Cuttlerat/zmk-config-lynxware-cat/img/IMG_1715.JPG

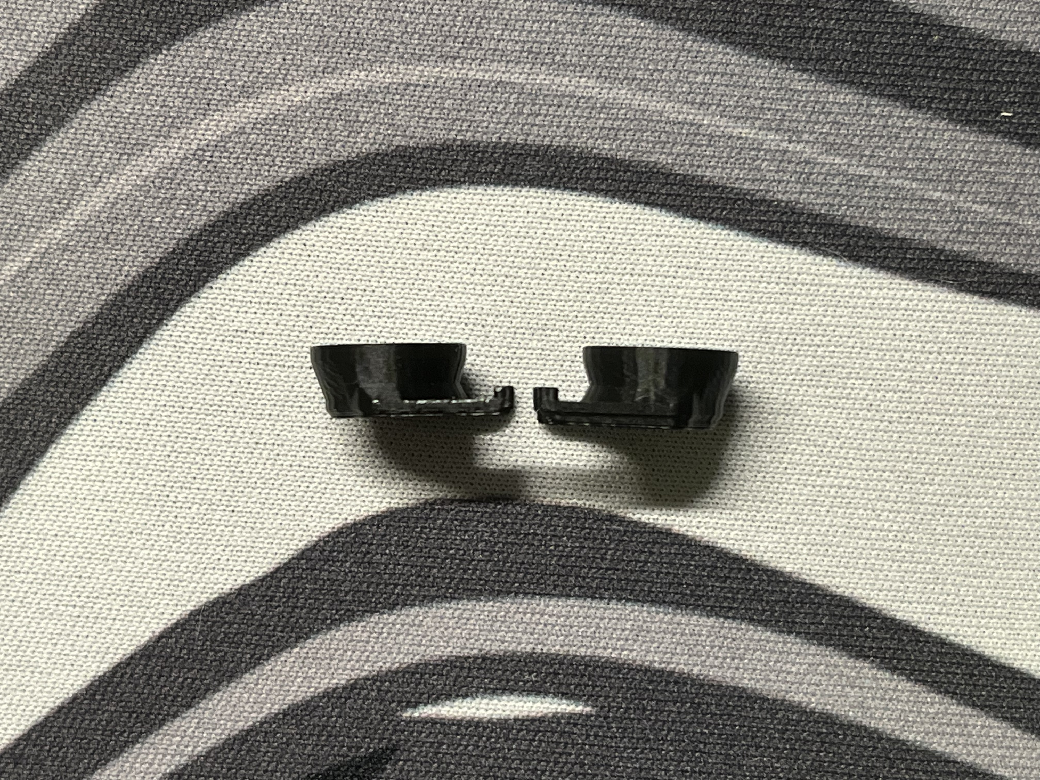
img/IMG_1715.JPG
