Cuttlerat/zmk-config-lynxware-cat/img/IMG_1717.JPG

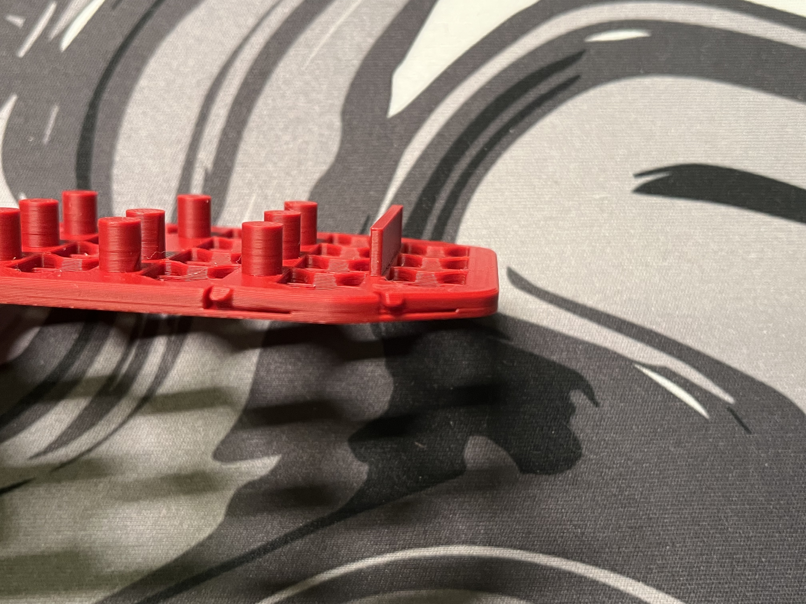
img/IMG_1717.JPG
