Cuttlerat/zmk-config-lynxware-cat/img/IMG_1721.JPG

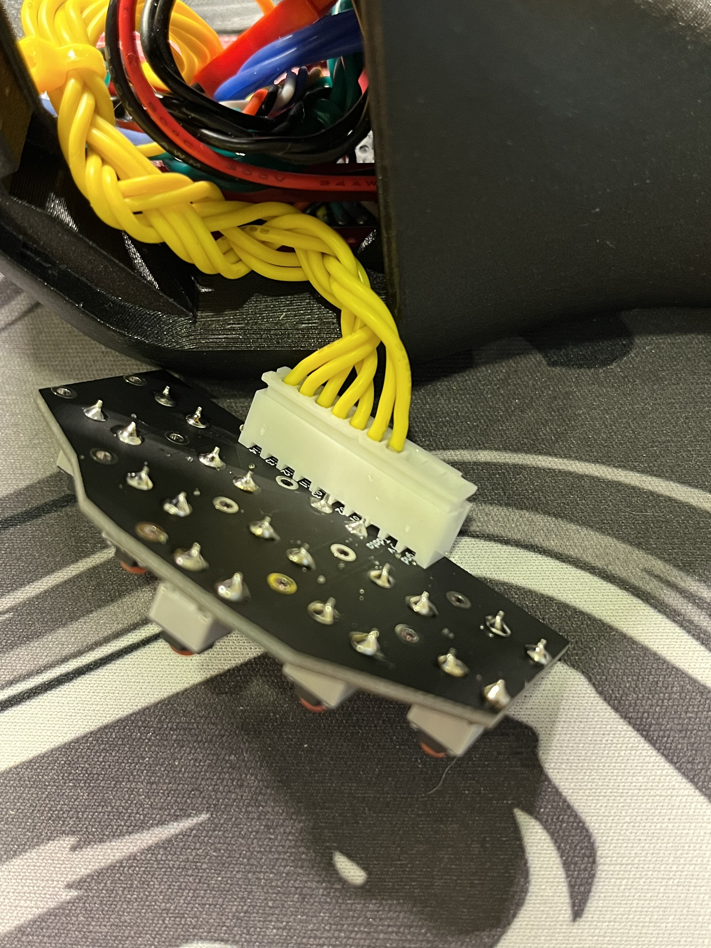
img/IMG_1721.JPG
