Cuttlerat/zmk-config-lynxware-cat/img/IMG_1724.JPG

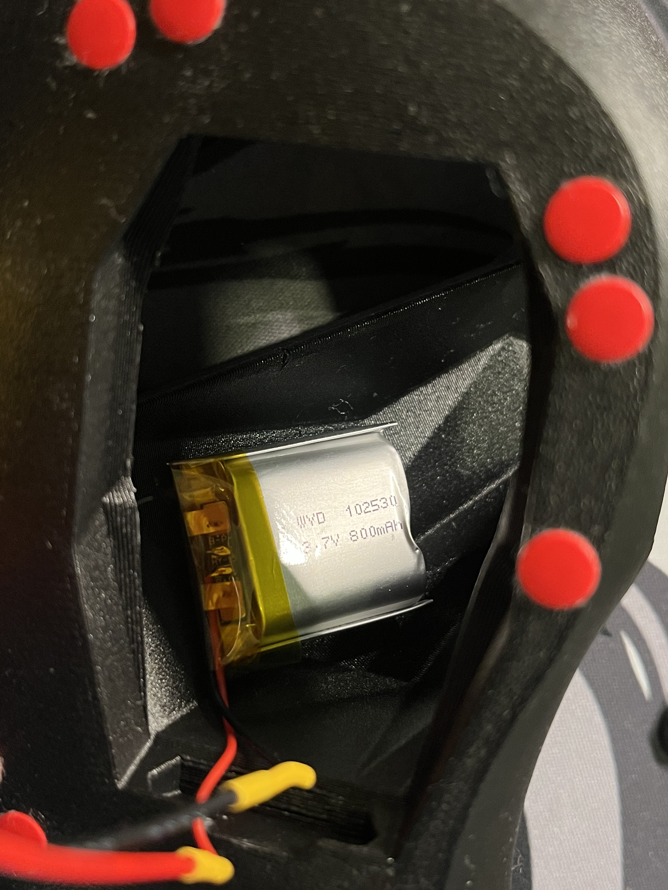
img/IMG_1724.JPG
