Cuttlerat/zmk-config-lynxware-cat/img/IMG_1726.JPG

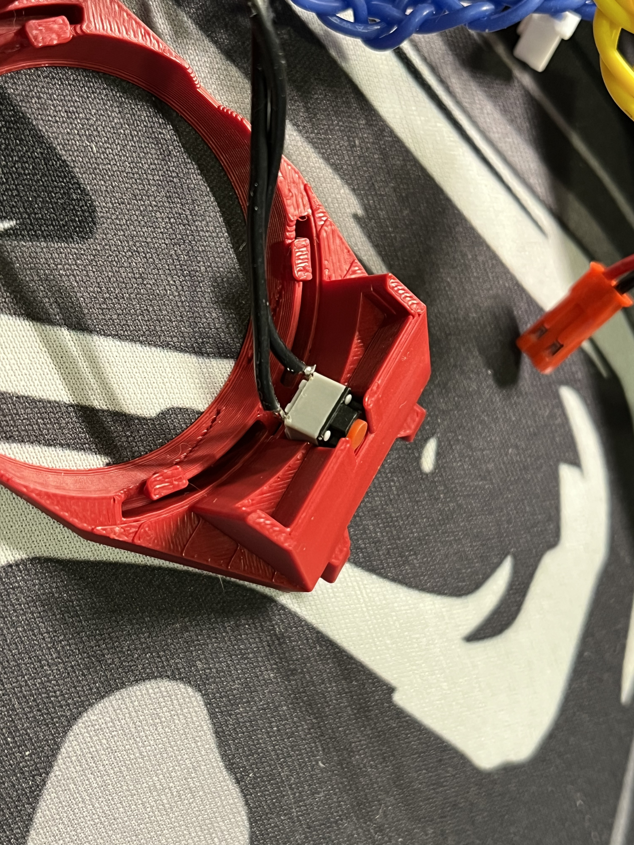
img/IMG_1726.JPG
