Cuttlerat/zmk-config-lynxware-cat/img/IMG_1730.JPG

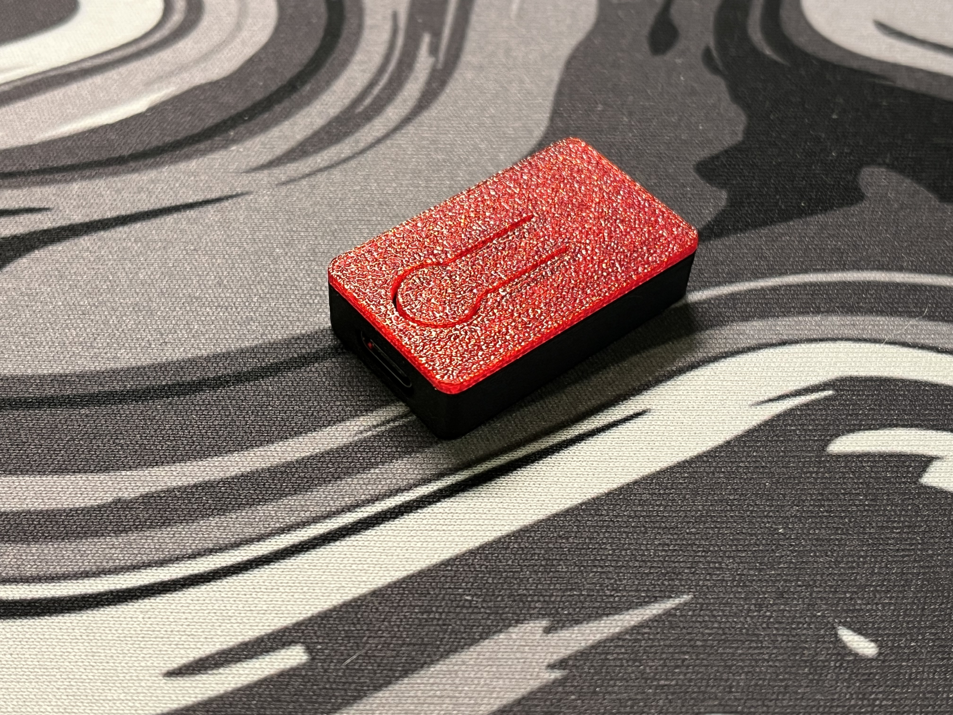
img/IMG_1730.JPG
