Cuttlerat/zmk-config-lynxware-cat/img/IMG_1732.JPG

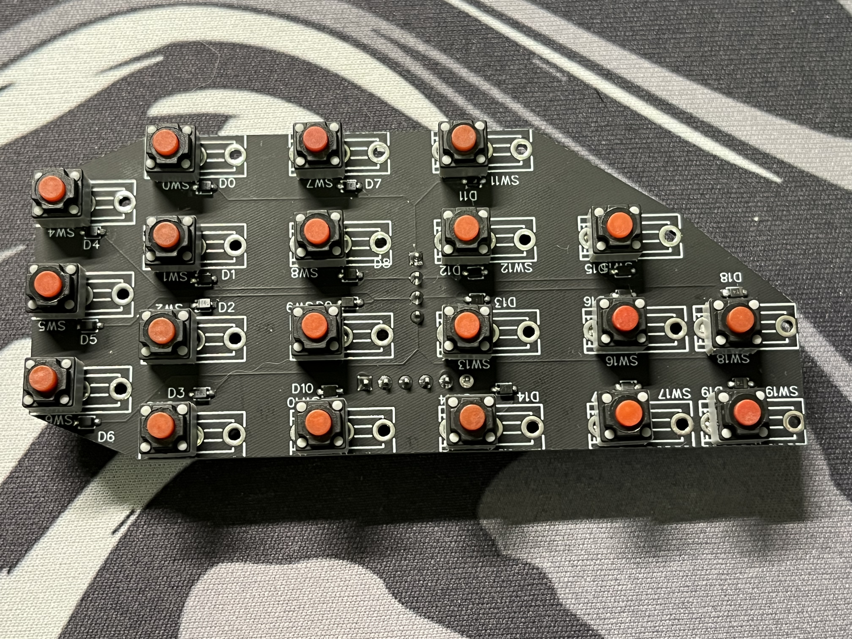
img/IMG_1732.JPG
