Cuttlerat/zmk-config-lynxware-cat/img/IMG_1733.JPG

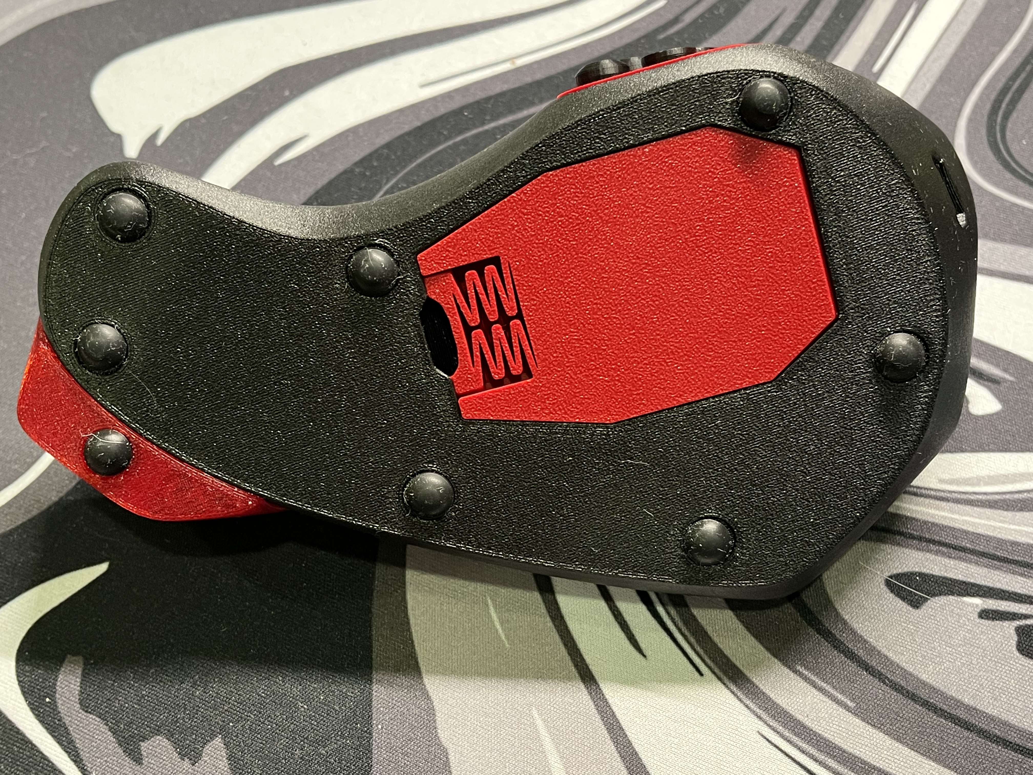
img/IMG_1733.JPG
