Cuttlerat/zmk-config-lynxware-cat/img/IMG_1734.JPG

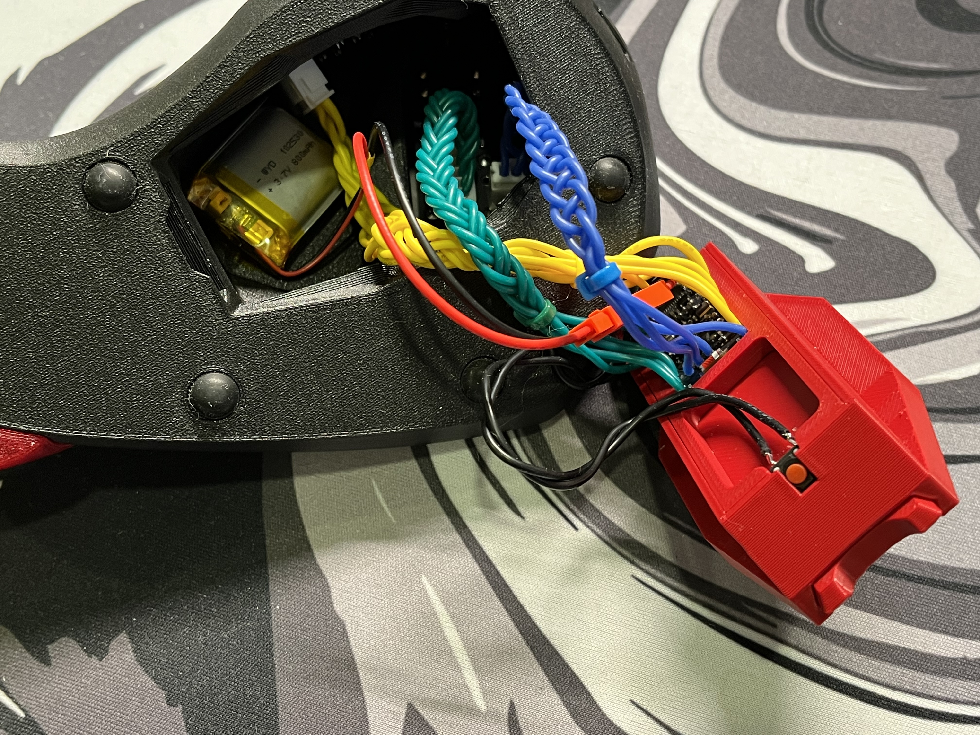
img/IMG_1734.JPG
