Cuttlerat/zmk-config-lynxware-cat/img/IMG_1735.JPG

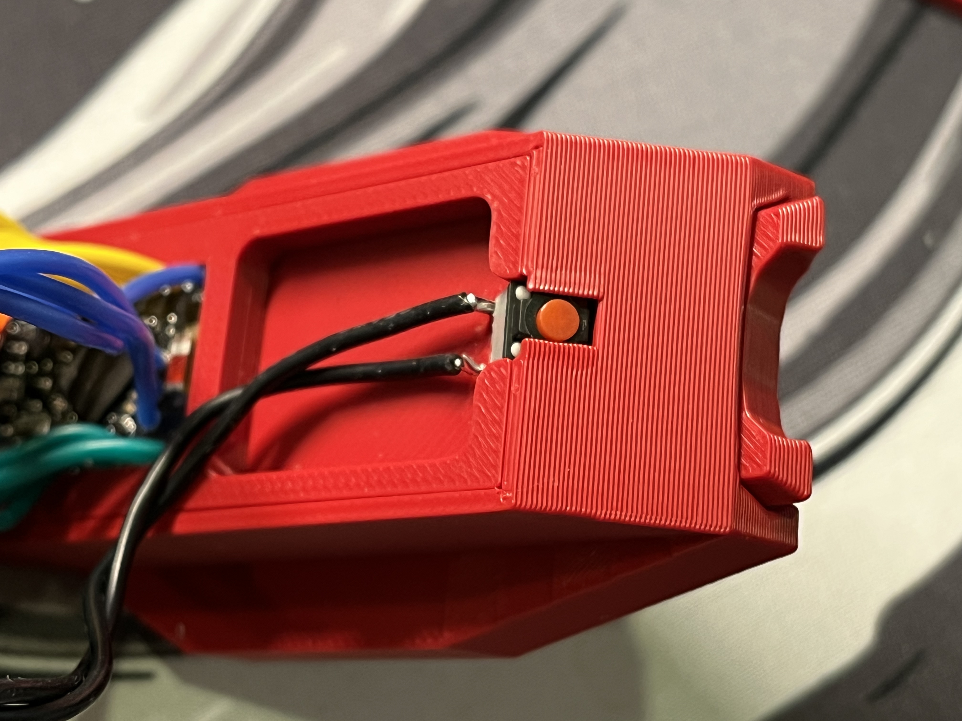
img/IMG_1735.JPG
