Cuttlerat/zmk-config-lynxware-cat/img/IMG_1719.JPG

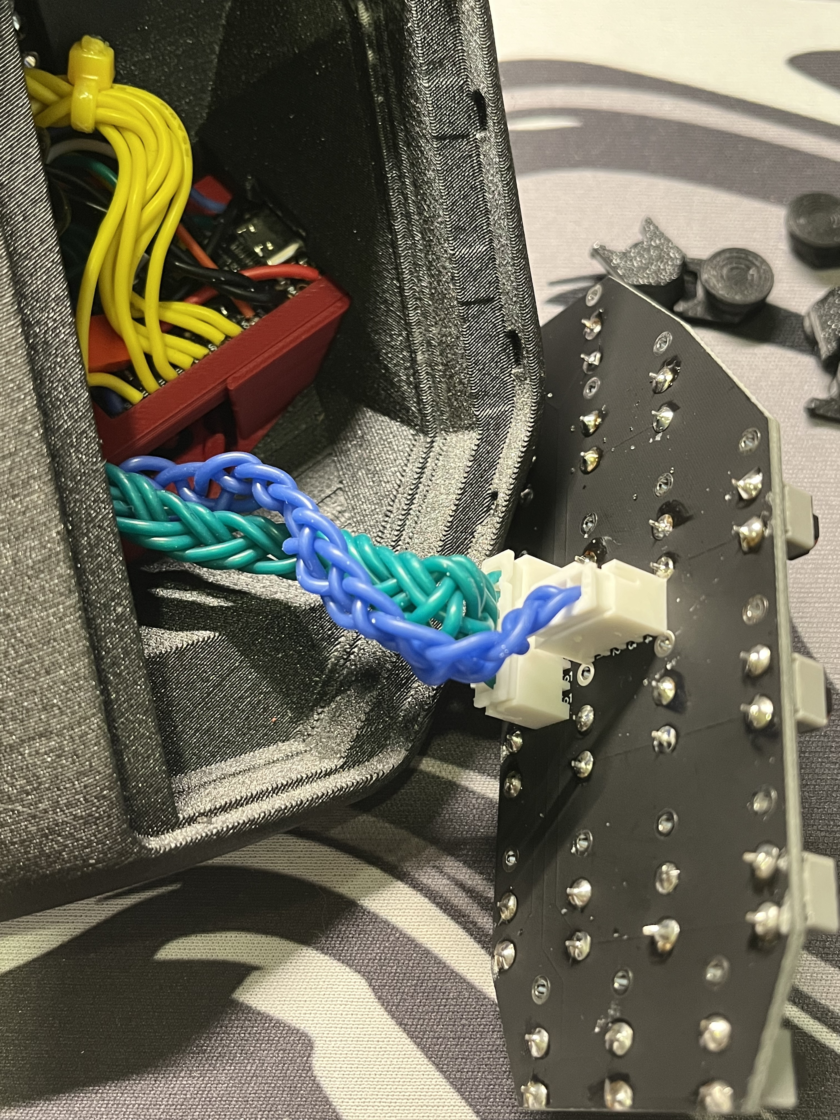
img/IMG_1719.JPG
