Cuttlerat/zmk-config-lynxware-cat/img/IMG_1722.JPG

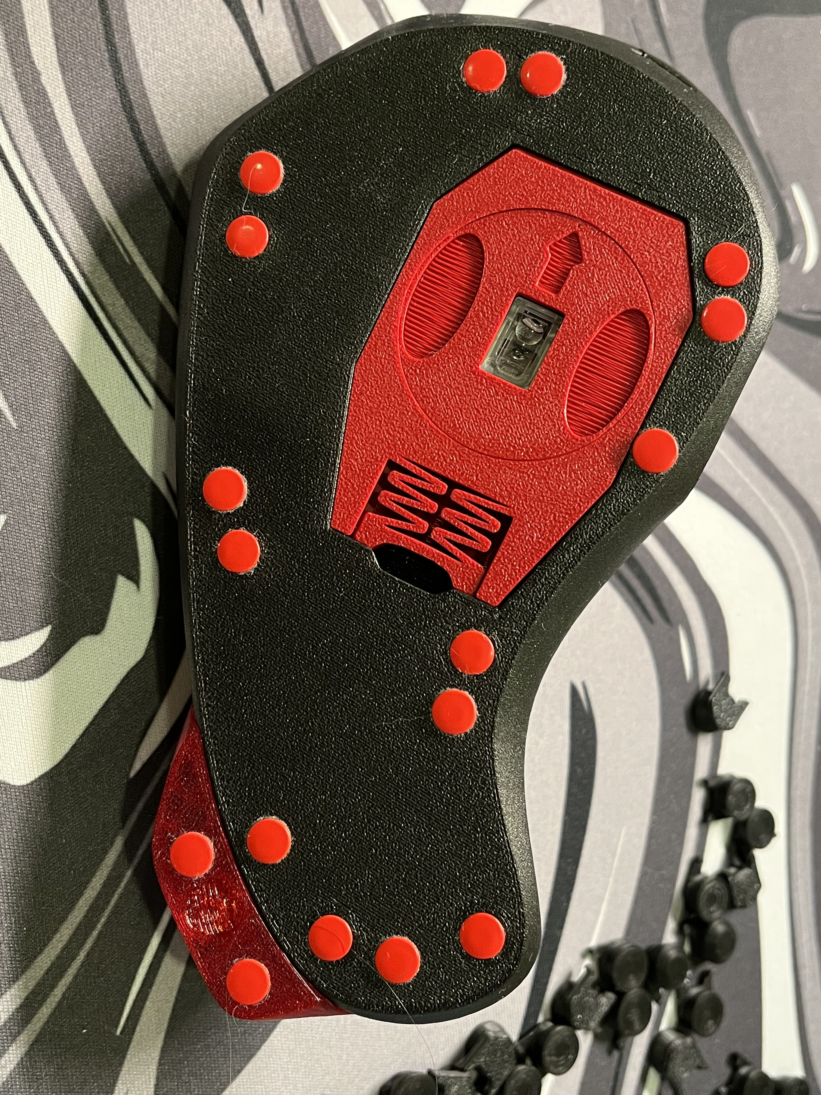
img/IMG_1722.JPG
