Cuttlerat/zmk-config-lynxware-cat/img/IMG_1723.JPG

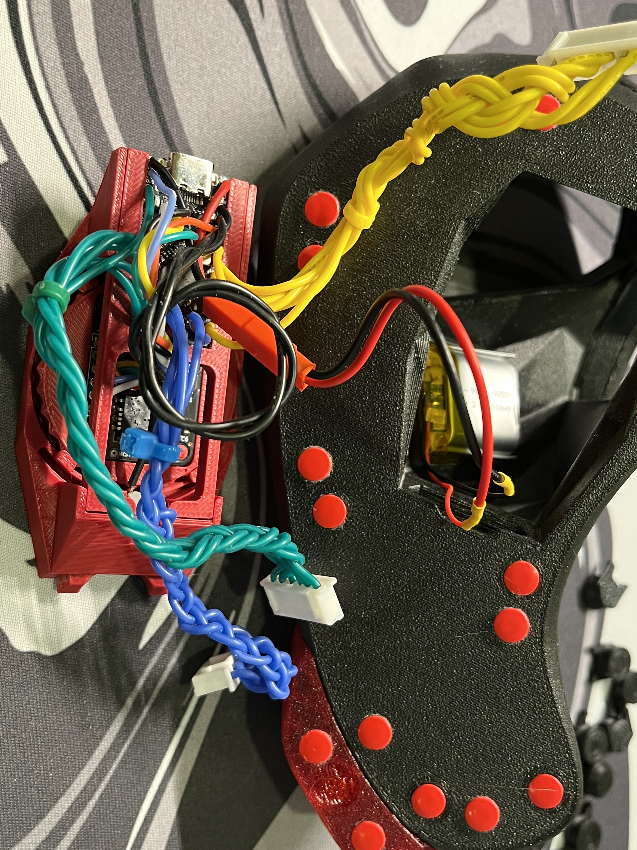
img/IMG_1723.JPG
