Cuttlerat/zmk-config-lynxware-cat/img/IMG_1725.JPG

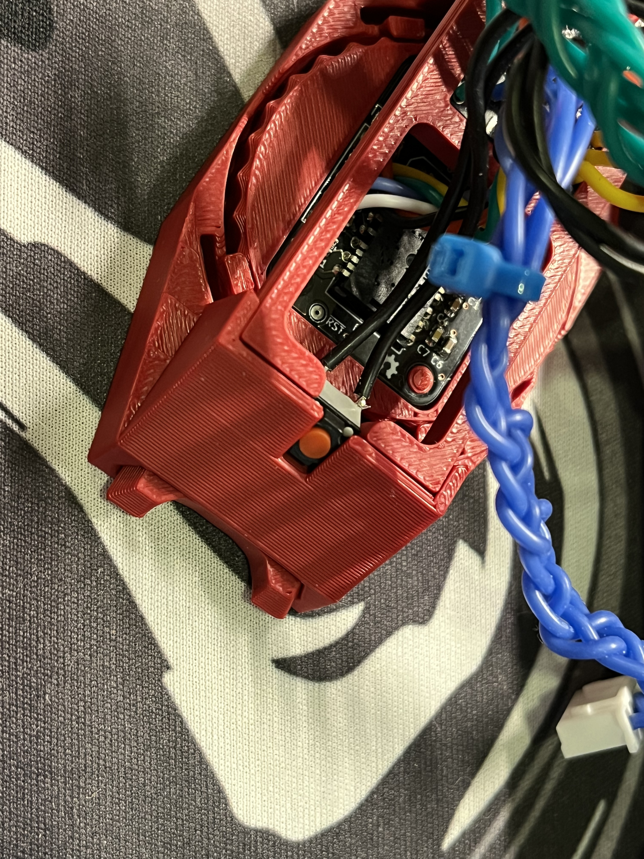
img/IMG_1725.JPG
